jp3cyc/versaWriter/circuit/verseWriter.sch

## KiCad design circuit/verseWriter.sch (2017-04-01)

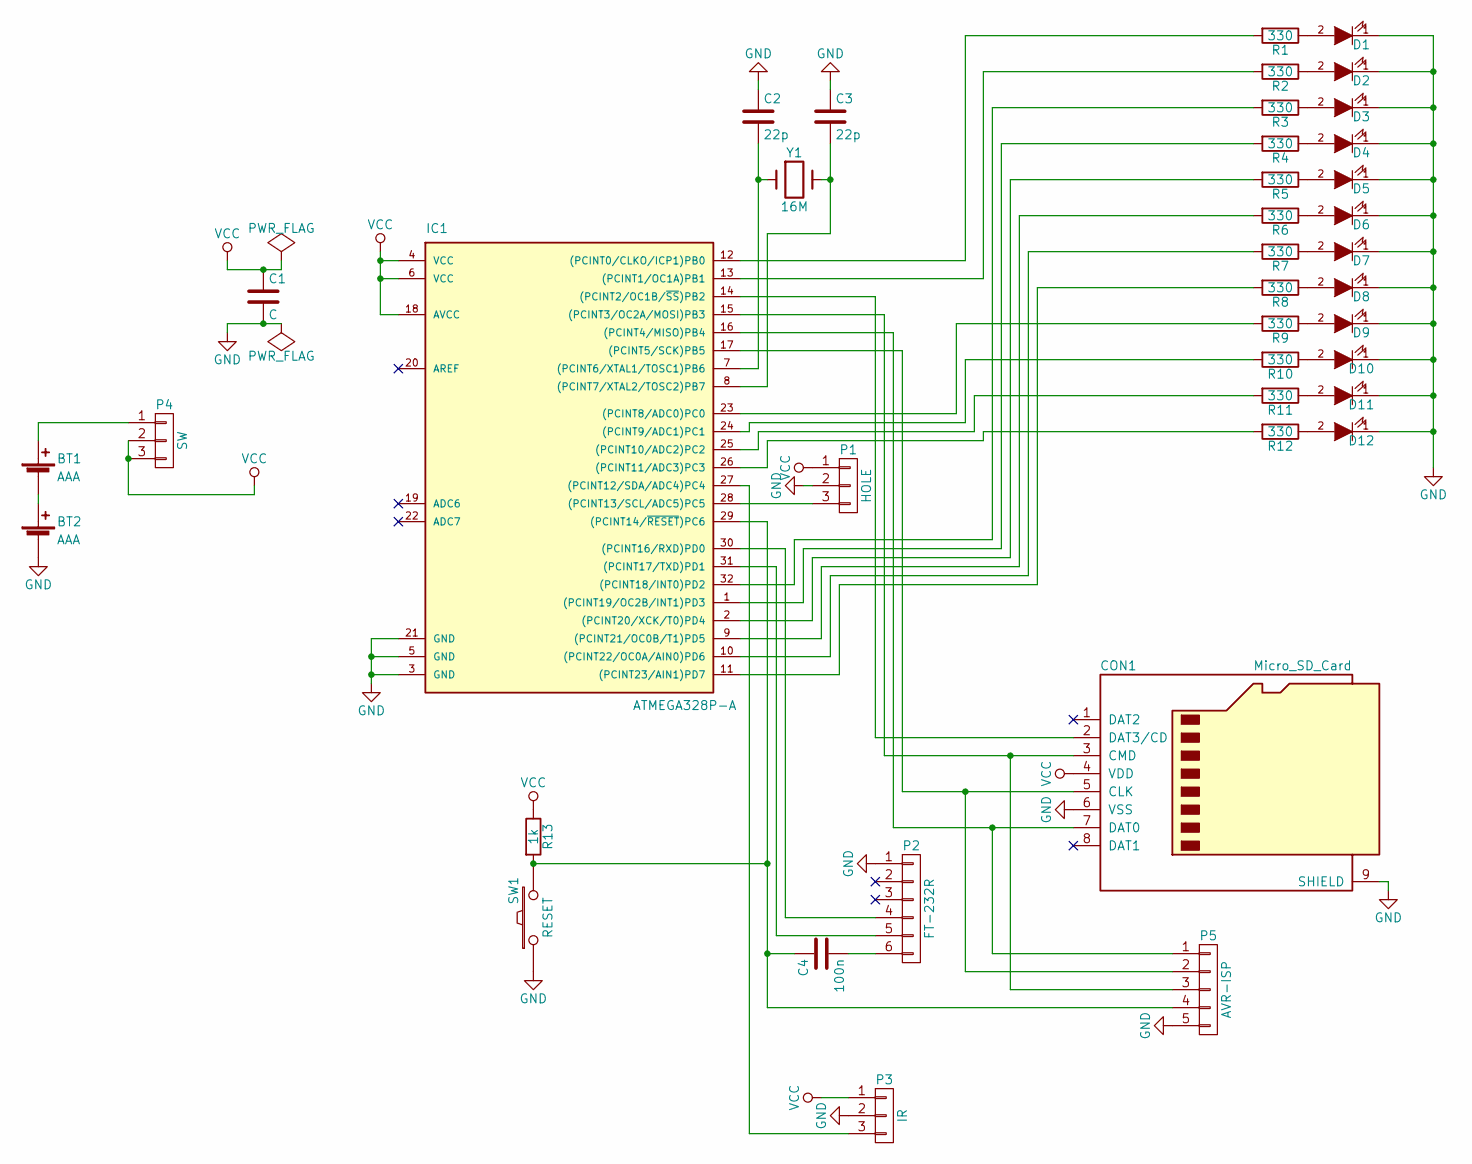
[picture p3: schematic verseWriter.sch]

Parts:
BT1, BT2: AAA
C1: C; C_0603
C2, C3: 22p; C_0603
C4: 100n; C_0603
CON1: Micro_SD_Card; HIROSE-MICROSD-DM3AT-SF
D1, D2, D3, D4, D5, D6, D7, D8, D9, D10, D11, D12: LED; LED_0805
IC1: ATMEGA328P-A; TQFP-32_7x7mm_Pitch0.8mm
P1: HOLE; Pin_Header_Straight_1x03_Pitch2.54mm
P2: FT-232R; Pin_Header_Straight_1x06_Pitch2.54mm
P3: IR; Pin_Header_Straight_1x03_Pitch2.54mm
P4: SW; Pin_Header_Straight_1x03_Pitch2.54mm
P5: AVR-ISP; Pin_Header_Straight_1x05_Pitch2.54mm
R1, R2, R3, R4, R5, R6, R7, R8, R9, R10, R11, R12: 330; R_0805
R13: 1k; R_0805
SW1: RESET; SW_SPST_KMR2
Y1: 16M; Crystal_HC18-U_Vertical

Connections:
GND: BT2.2 (-), C1.2, C2.1, C3.1, CON1.6 (VSS), CON1.9 (SHIELD), D1.1 (K), D2.1 (K), D3.1 (K), D4.1 (K), D5.1 (K), D6.1 (K), D7.1 (K), D8.1 (K), D9.1 (K), D10.1 (K), D11.1 (K), D12.1 (K), IC1.3 (GND), IC1.5 (GND), IC1.21 (GND), P1.2, P2.1, P3.2, P5.5, SW1.1
unnamed: BT1.1 (+), P4.1
unnamed: BT1.2 (-), BT2.1 (+)
unnamed: C2.2, IC1.7 ((PCINT6/XTAL1/TOSC1)PB6), Y1.1
unnamed: C3.2, IC1.8 ((PCINT7/XTAL2/TOSC2)PB7), Y1.2
unnamed: C4.1, IC1.29 ((PCINT14/~RESET~)PC6), P5.4, R13.2, SW1.2
unnamed: C4.2, P2.6
unnamed: CON1.2 (DAT3/CD), IC1.14 ((PCINT2/OC1B/~SS~)PB2)
unnamed: CON1.3 (CMD), IC1.15 ((PCINT3/OC2A/MOSI)PB3), P5.3
unnamed: CON1.5 (CLK), IC1.17 ((PCINT5/SCK)PB5), P5.2
unnamed: CON1.7 (DAT0), IC1.16 ((PCINT4/MISO)PB4), P5.1
unnamed: D1.2 (A), R1.1
unnamed: D2.2 (A), R2.1
unnamed: D3.2 (A), R3.1
unnamed: D4.2 (A), R4.1
unnamed: D5.2 (A), R5.1
unnamed: D6.2 (A), R6.1
unnamed: D7.2 (A), R7.1
unnamed: D8.2 (A), R8.1
unnamed: D9.2 (A), R9.1
unnamed: D10.2 (A), R10.1
unnamed: D11.2 (A), R11.1
unnamed: D12.2 (A), R12.1
unnamed: IC1.1 ((PCINT19/OC2B/INT1)PD3), R4.2
unnamed: IC1.2 ((PCINT20/XCK/T0)PD4), R5.2
unnamed: IC1.9 ((PCINT21/OC0B/T1)PD5), R6.2
unnamed: IC1.10 ((PCINT22/OC0A/AIN0)PD6), R7.2
unnamed: IC1.11 ((PCINT23/AIN1)PD7), R8.2
unnamed: IC1.12 ((PCINT0/CLKO/ICP1)PB0), R1.2
unnamed: IC1.13 ((PCINT1/OC1A)PB1), R2.2
unnamed: IC1.23 ((PCINT8/ADC0)PC0), R9.2
unnamed: IC1.24 ((PCINT9/ADC1)PC1), R10.2
unnamed: IC1.25 ((PCINT10/ADC2)PC2), R11.2
unnamed: IC1.26 ((PCINT11/ADC3)PC3), R12.2
unnamed: IC1.27 ((PCINT12/SDA/ADC4)PC4), P3.3
unnamed: IC1.28 ((PCINT13/SCL/ADC5)PC5), P1.3
unnamed: IC1.30 ((PCINT16/RXD)PD0), P2.4
unnamed: IC1.31 ((PCINT17/TXD)PD1), P2.5
unnamed: IC1.32 ((PCINT18/INT0)PD2), R3.2
VCC: C1.1, CON1.4 (VDD), IC1.4 (VCC), IC1.6 (VCC), IC1.18 (AVCC), P1.1, P3.1, P4.2, P4.3, R13.1
